telzo2000/jisaku20/img/img00002.jpg

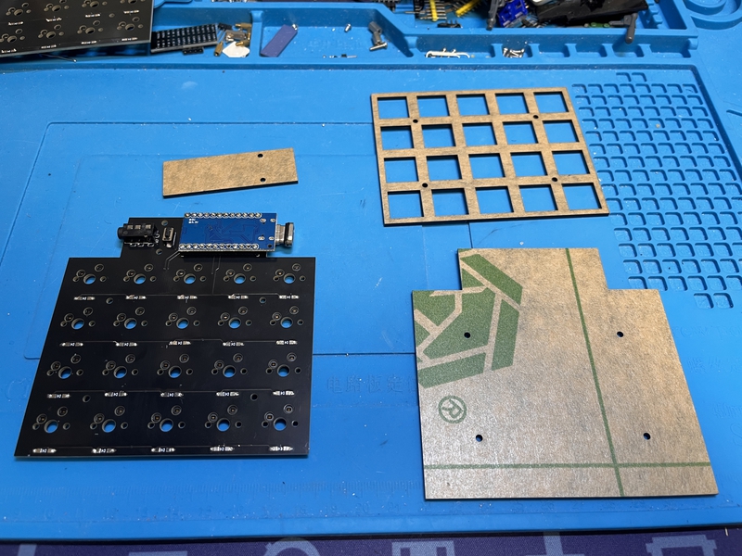
img/img00002.jpg
