telzo2000/jisaku20/img/img00008.jpg

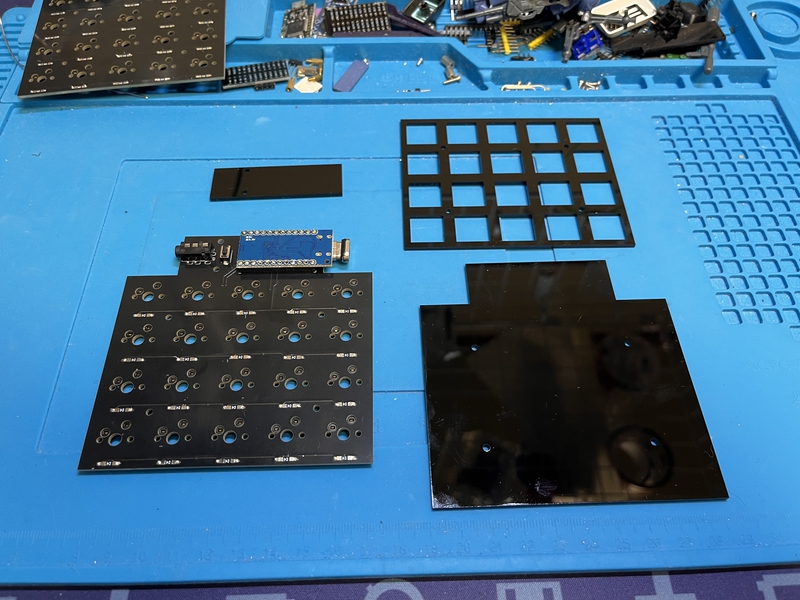
img/img00008.jpg
