telzo2000/jisaku20/img/img00014.jpg

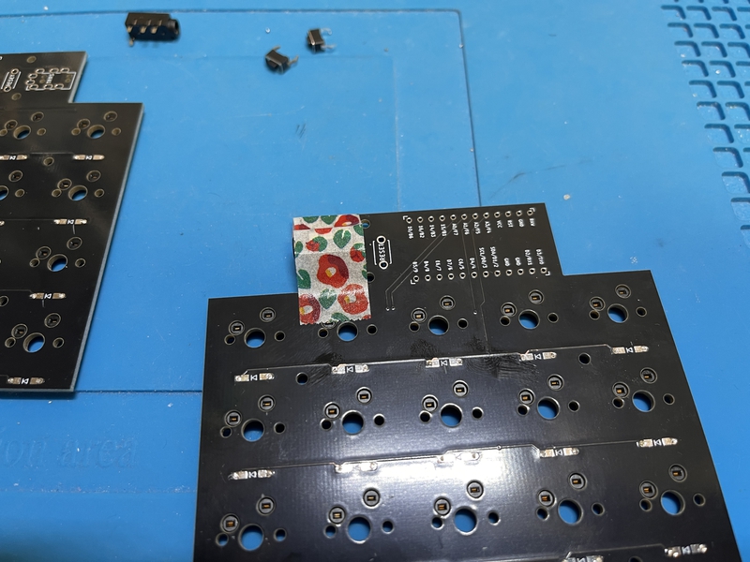
img/img00014.jpg
