telzo2000/jisaku20/img/img00016.jpg

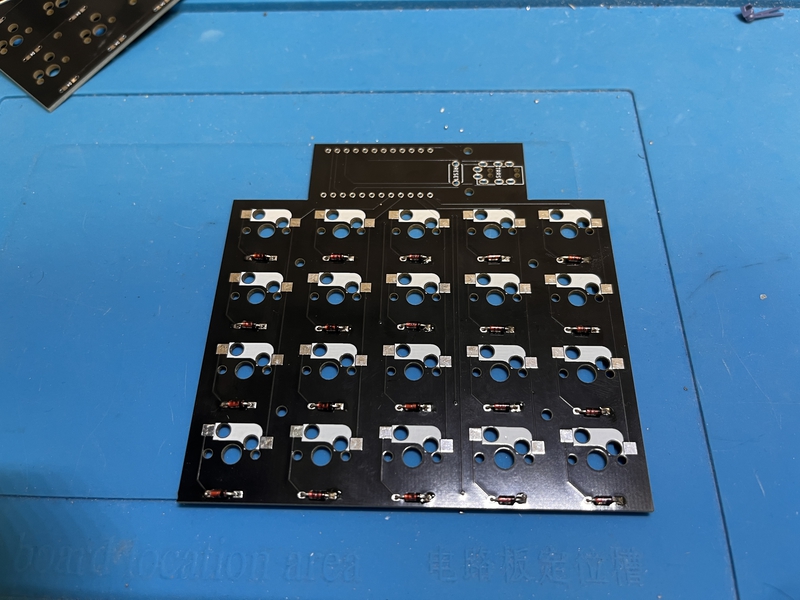
img/img00016.jpg
