telzo2000/jisaku20/img/img00018.jpg

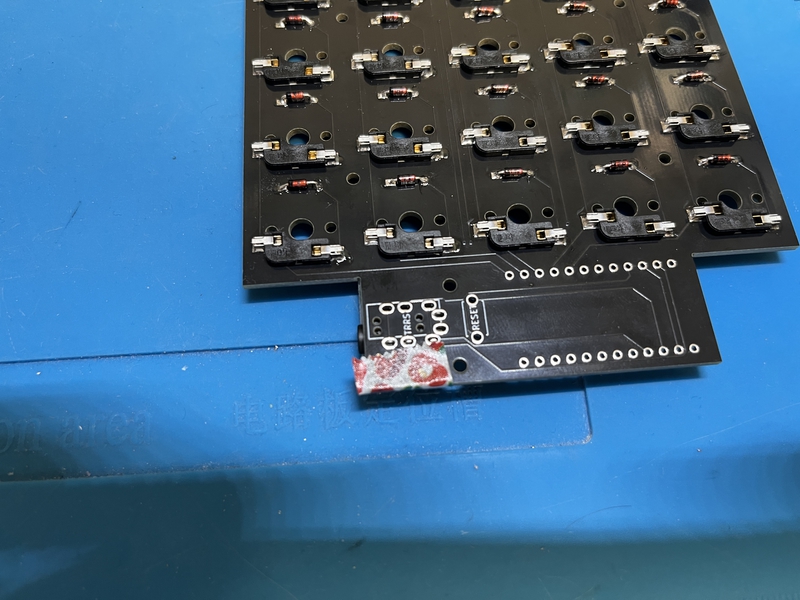
img/img00018.jpg
