telzo2000/jisaku20/img/img00019.jpg

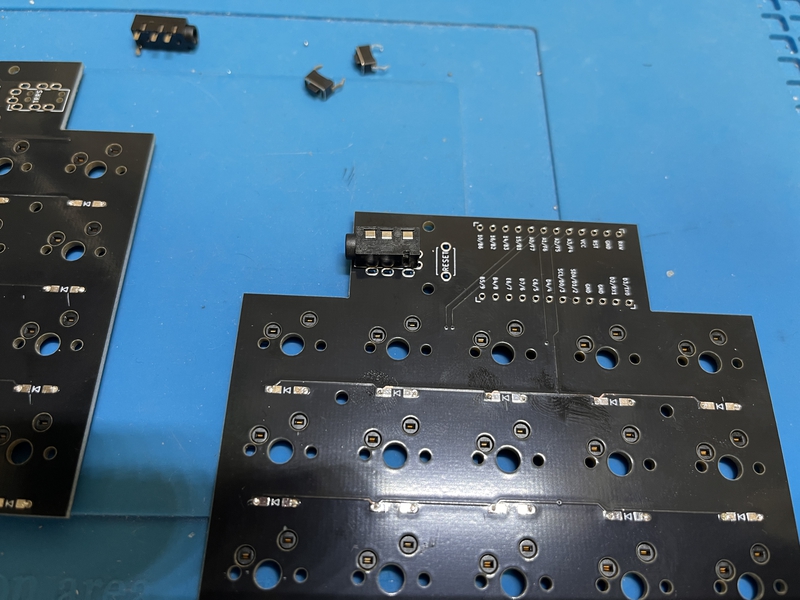
img/img00019.jpg
