telzo2000/jisaku20/img/img00020.jpg

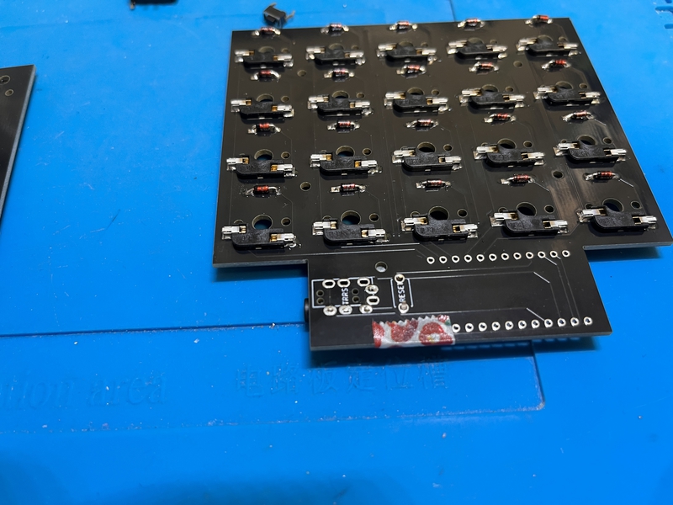
img/img00020.jpg
