telzo2000/jisaku20/img/img00021.jpg

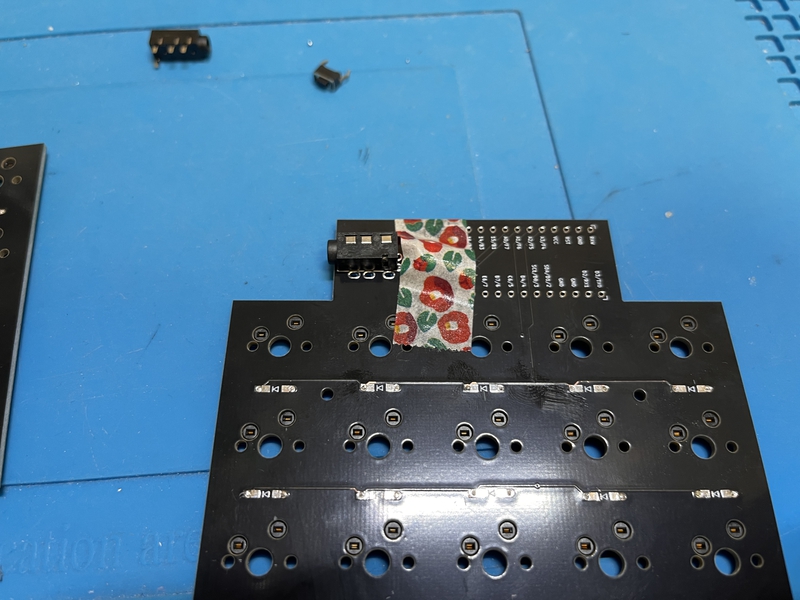
img/img00021.jpg
