telzo2000/jisaku20/firmware/jisaku20rp_right_re/keymaps/vial/config.h

// Copyright 2023 m.ki (@telzo2000)
// SPDX-License-Identifier: GPL-2.0-or-later

#pragma once
#define VIAL_KEYBOARD_UID {0x07, 0x87, 0xF6, 0x2A, 0x6F, 0x7D, 0x6F, 0xF1}
#define VIAL_UNLOCK_COMBO_ROWS { 1, 0 }
#define VIAL_UNLOCK_COMBO_COLS { 0, 1 }
